sideburn/fujinet-xebook-kicad/Fab/as-built-1.0-PCBWay-T-1D22W845207A/Edits to PCBway/T-1D22W845207A/位号：J_SIO1,确认方向.png

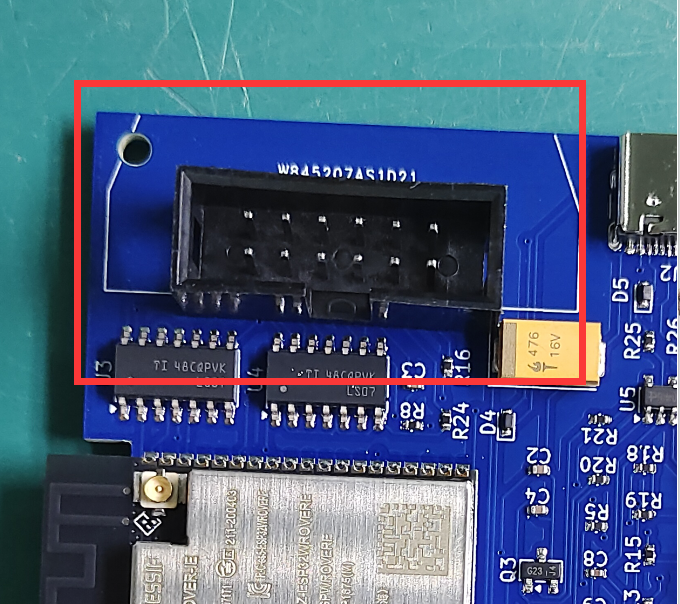
Fab/as-built-1.0-PCBWay-T-1D22W845207A/Edits to PCBway/T-1D22W845207A/位号：J_SIO1,确认方向.png
