sideburn/fujinet-xebook-kicad/Fab/as-built-1.0-PCBWay-T-1D22W845207A/Edits to PCBway/T-1D22W845207A_EQPic_0812140108/3_202608121354364093316.jpg

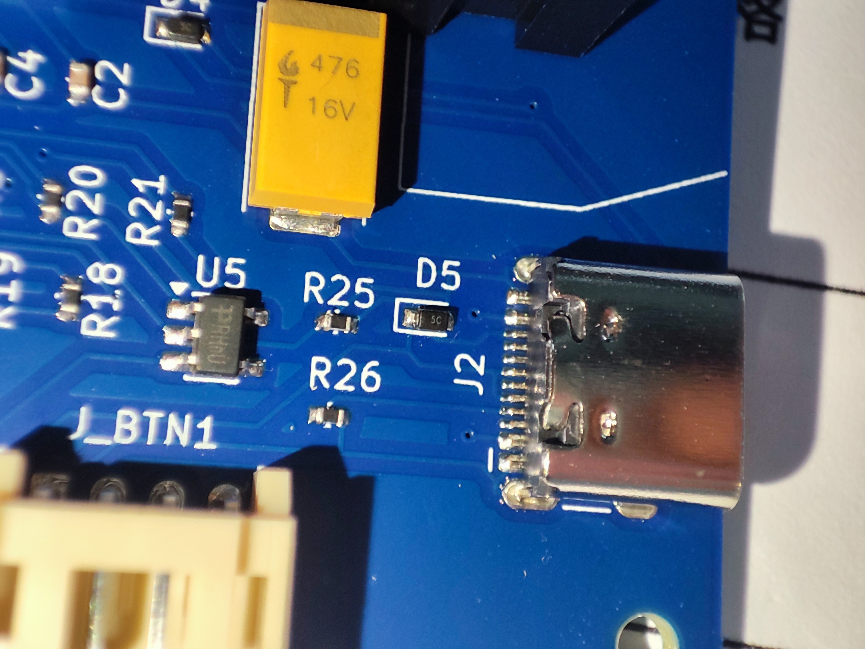
Fab/as-built-1.0-PCBWay-T-1D22W845207A/Edits to PCBway/T-1D22W845207A_EQPic_0812140108/3_202608121354364093316.jpg
