sideburn/fujinet-xebook-kicad/Graphics/PCBTop.png

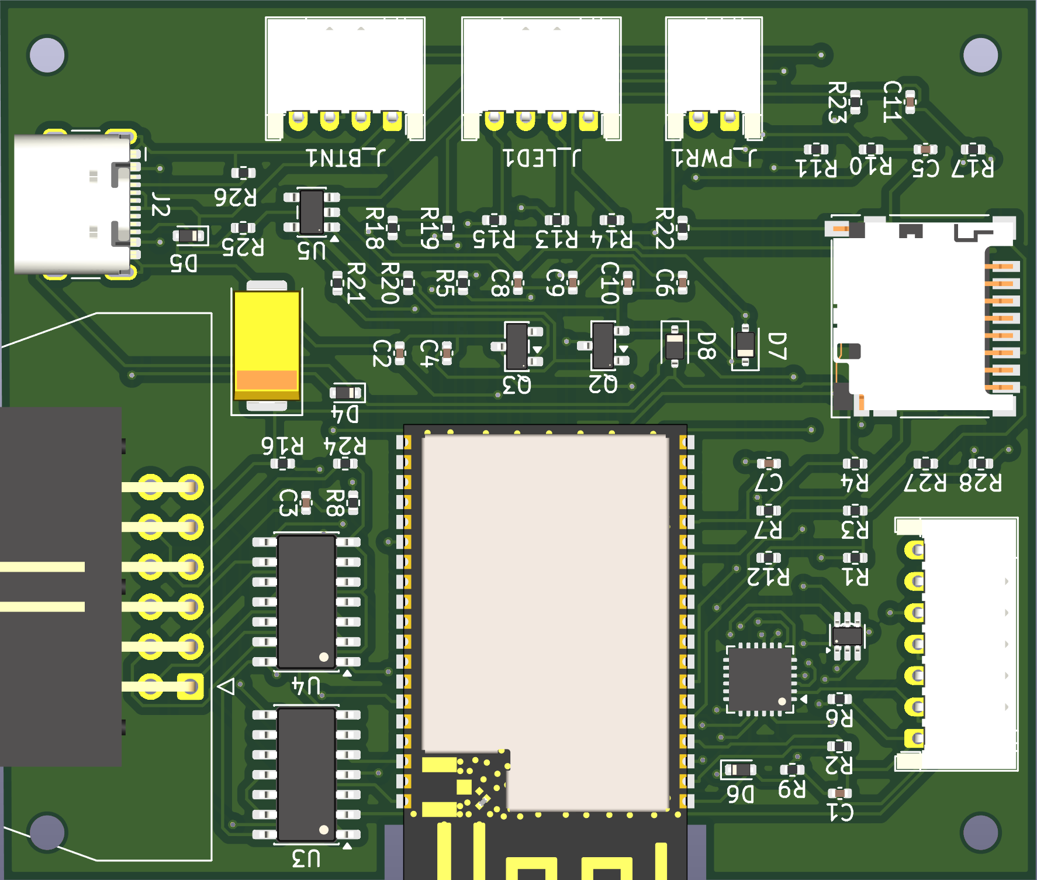
Graphics/PCBTop.png
